firefly/wallet/source/firefly/firefly_fonts.h

#include <avr/pgmspace.h>

const uint32_t font_big[] PROGMEM = {
    0xc3c77e3c, 0xcfdbf3e3, 0x3c7ee3c7, 0x1e1e1c18,
    0x18181818, 0xffff1818, 0xc0e67e3c, 0x1c3060c0,
    0xffff060e, 0xc0c37f3e, 0xe0783860, 0x3e7fc3c0,
    0x1c183030, 0x6366660c, 0x6060ffff, 0x0303ffff,
    0xc0e07f3f, 0x3e7fe3c0, 0x03c6fe7c, 0xc3ff7f03,
    0x3c7ec3c3, 0xc0c3ffff, 0x30306060, 0x18181818,
    0xc3c37e3c, 0xc3663c66, 0x3c7ec3c3, 0xc3c37e3c,
    0xc0fcfec3, 0x3c7ec6c0, 0x663c3c18, 0xffff6666,
    0xc3c3c3c3, 0xc6c67f3f, 0xc67e7ec6, 0x3f7fc6c6,
    0x03c7fe7c, 0x03030303, 0x7cfec703, 0xc3e37f1f,
    0xc3c3c3c3, 0x3f7fe3c3, 0x0303ffff, 0x033f3f03,
    0xffff0303, 0x0303ffff, 0x033f3f03, 0x03030303,
    0x00000000, 0x3c7ee7c3, 0xc3e77e3c, 0x00c3ff00,
    0x007e0000, 0xffc30000, 0x428181ff, 0x24181824,
    0xffb59942
};


const uint32_t font_small[] PROGMEM = {
    0x7e91897e, 0x8486ff80, 0xc2a1918e, 0x42898976,
    0x1e10ff10, 0x4f898971, 0x7e898972, 0x0101f10f,
    0x76898976, 0x4e91917e, 0xff898976, 0x0f08f80f,
    0x0101ff01, 0xff898981, 0x46898972, 0x78848478,
    0xff205088, 0x02b10906
};


const uint8_t font_tiny[] PROGMEM = {
    0x05, 0xc0, 0x30, 0x0f, 0xea, 0xf9, 0x7e, 0xa9, 0x11, 0x3c,
    0xbb, 0xc0, 0x30, 0x45, 0xc0, 0x03, 0xa2, 0x51, 0x14, 0x8e,
    0x20, 0x11, 0x02, 0x10, 0x80, 0x80, 0x06, 0x4c, 0x3e, 0x3e,
    0x07, 0xc5, 0x2a, 0xe5, 0x55, 0x8f, 0xc8, 0x74, 0xd6, 0xfd,
    0xaf, 0x86, 0x5c, 0xfe, 0xbf, 0x7d, 0x6e, 0x05, 0x00, 0x0a,
    0x84, 0x54, 0x45, 0x29, 0x44, 0x54, 0x47, 0x50, 0xda, 0xae,
    0xf1, 0x7c, 0xaa, 0xfe, 0x31, 0x73, 0xa3, 0xfa, 0xd7, 0xe5,
    0x2f, 0xfb, 0x57, 0x7c, 0x9f, 0x8f, 0xe2, 0xf8, 0x23, 0x64,
    0xfc, 0x21, 0xff, 0x9b, 0xff, 0x77, 0xdd, 0x17, 0x08, 0xbf,
    0xf6, 0x5d, 0x66, 0xfd, 0x35, 0x90, 0x7e, 0x1f, 0xc1, 0xe7,
    0xc1, 0xfe, 0xcf, 0xec, 0x9b, 0x1f, 0x07, 0x3a, 0xe6, 0x31,
    0xfa, 0x08, 0x2f, 0xc6, 0x22, 0x08, 0xa1, 0x08, 0x00, 0x41,
    0xe5, 0xb4, 0xc9, 0x7e, 0x52, 0x67, 0xe4, 0xcb, 0x69, 0x85,
    0xf1, 0x3c, 0xa6, 0x70, 0x5f, 0x07, 0x41, 0xd0, 0x42, 0x4c,
    0xfc, 0x3f, 0x1f, 0x3b, 0xdc, 0x17, 0x99, 0x26, 0x32, 0x5e,
    0xf4, 0x98, 0x21, 0x71, 0x5e, 0xa4, 0xbe, 0x2f, 0x41, 0xce,
    0xc3, 0xbd, 0xcf, 0x49, 0x92, 0xf2, 0x0d, 0x6f, 0x6a, 0x3b,
    0x20, 0x36, 0x02, 0x6e, 0x21, 0x18, 0xbf, 0x84, 0x00
};
